sysuwilliam/NC-Current-Source/测试/恒压源测试/markdown/4.23周四晚上测试.md

测试记录：

- 最开始用了15VVIN，后面都是用5V

- Boot输出为0

- 把tps5450短路，VOUT正常输出VIN的值

- 采样电路的两个排针都有输出，只是不符合预期的比例

- 换了一次tps5450芯片，现象没有变化（是这样吗？有点记不清

需要细节补充：

- 降压芯片的引脚只测了boot吗？PH和VSENSE都没测吗？

（备注：严格来说PH是真正的输出端，输出0/Vin的方波；boot是在PH基础上加一个由内部LDO提供的6-8V的电压Vldo，用于芯片内部的自举驱动，正常情况下输出Vldo/Vin+Vldo的方波）

问题分析：

- 主要问题：tps5450输入电压范围在5.5V到36V，5V输入会导致欠压锁定

-
